waicool20/Divergence-Meter-Project/Software/Display.c

/*  GPLv3 License
 *  
 *  	Copyright (c) Divergence Meter Project by waicool20
 *  	
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
 *  You should have received a copy of the GNU General Public License
 *  along with this program.  If not, see <http://www.gnu.org/licenses/>.
 */

/*
 * This is the main display code which handles displaying the digits onto the nixie tube.
 * Numbers 0-11 can be written directly into the variables tube(1-8) and the display will be updated
 * once the updateDisplay() function is called.
 */

#include <avr/io.h>
#include <avr/pgmspace.h>
#include "Display.h"
#include "ShiftRegister.h"
#include "Constants.h"

char tube1 = 0;
char tube2 = 0;
char tube3 = 0;
char tube4 = 0;
char tube5 = 0;
char tube6 = 0;
char tube7 = 0;
char tube8 = 0;

unsigned char brightness = 10;
const unsigned char brightnessLevels[11] PROGMEM = {0,25,50,75,100,125,150,175,200,225,250};

void initDisplay() {
  //Clear shift registers
  SRSendZeros(96);
  SRLatch();

  //Setup Timer1 with Fast PWM mode with x1 prescaler
  TCCR1A |= (1<<COM1A1) | (1<<PWM1A);
  TCCR1B |= (1<<CS10);
  OCR1A = pgm_read_byte(&(brightnessLevels[brightness]));
}

void handleShiftRegister1() {
  switch (tube6) {
    case 1:
    case 2:
    case 3:
      SRSendZeros(8);
      break;
    case 0:
      SRSendZeros(6);
      SRSendOnes(1);
      SRSendZeros(1);
      break;
    case RDP:
      SRSendZeros(7);
      SRSendOnes(1);
      break;
    default:
      SRSendZeros(tube6 - 4);
      SRSendOnes(1);
      SRSendZeros(11 - tube6);
      break;
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
  SRLatch();
}

void increaseDisplayBrightness(){
  if(brightness < 10){
    brightness++;
    OCR1A = pgm_read_byte(&(brightnessLevels[brightness]));
  }
}

void decreaseDisplayBrightness(){
  if(brightness > 0){
    brightness--;
    OCR1A = pgm_read_byte(&(brightnessLevels[brightness]));
  }
}
